larsthmn/gameshow-buzzer/src/credentials.h

//
// Created by Lars on 10.05.2024.
//

#ifndef ESP32_BUZZER_CREDENTIALS_H
#define ESP32_BUZZER_CREDENTIALS_H

#define WIFI_SSID "ssid"
#define WIFI_PASSWORD "password"
#define FTP_USER     "ftp"
#define FTP_PASSWORD "ftp"

#endif //ESP32_BUZZER_CREDENTIALS_H
