larsthmn/gameshow-buzzer/samples/audioplayback.cpp

//
// Created by Lars on 04.05.2024.
//

#if 0
#include "audioplayback.h"

#include "Arduino.h"
#include "WiFi.h"
#include "Audio.h"
#include "pins.h"

static Audio audio;

//****************************************************************************************
//                                   A U D I O _ T A S K                                 *
//****************************************************************************************

struct audioMessage{
   uint8_t     cmd;
   const char* txt;
   uint32_t    value;
   uint32_t    ret;
} audioTxMessage, audioRxMessage;

enum : uint8_t { SET_VOLUME, GET_VOLUME, CONNECTTOHOST, CONNECTTOSD };

QueueHandle_t audioSetQueue = NULL;
QueueHandle_t audioGetQueue = NULL;

static void CreateQueues(){
   audioSetQueue = xQueueCreate(10, sizeof(struct audioMessage));
   audioGetQueue = xQueueCreate(10, sizeof(struct audioMessage));
}

static void audioTask(void *parameter) {
   CreateQueues();
   if(!audioSetQueue || !audioGetQueue){
      log_e("queues are not initialized");
      while(true){;}  // endless loop
   }

   struct audioMessage audioRxTaskMessage;
   struct audioMessage audioTxTaskMessage;

   audio.setPinout(I2S_BCLK, I2S_LRC, I2S_DOUT);
   audio.setVolume(15); // 0...21

   while(true){
      if(xQueueReceive(audioSetQueue, &audioRxTaskMessage, 1) == pdPASS) {
         if(audioRxTaskMessage.cmd == SET_VOLUME){
            audioTxTaskMessage.cmd = SET_VOLUME;
            audio.setVolume(audioRxTaskMessage.value);
            audioTxTaskMessage.ret = 1;
            xQueueSend(audioGetQueue, &audioTxTaskMessage, portMAX_DELAY);
         }
         else if(audioRxTaskMessage.cmd == CONNECTTOHOST){
            audioTxTaskMessage.cmd = CONNECTTOHOST;
            audioTxTaskMessage.ret = audio.connecttohost(audioRxTaskMessage.txt);
            xQueueSend(audioGetQueue, &audioTxTaskMessage, portMAX_DELAY);
         }
         else if(audioRxTaskMessage.cmd == CONNECTTOSD){
            audioTxTaskMessage.cmd = CONNECTTOSD;
            audioTxTaskMessage.ret = audio.connecttoSD(audioRxTaskMessage.txt);
            xQueueSend(audioGetQueue, &audioTxTaskMessage, portMAX_DELAY);
         }
         else if(audioRxTaskMessage.cmd == GET_VOLUME){
            audioTxTaskMessage.cmd = GET_VOLUME;
            audioTxTaskMessage.ret = audio.getVolume();
            xQueueSend(audioGetQueue, &audioTxTaskMessage, portMAX_DELAY);
         }
         else{
            log_i("error");
         }
      }
      audio.loop();
      if (!audio.isRunning()) {
         sleep(1);
      }
   }
}

void audioInit() {
//   xTaskCreatePinnedToCore(
//      audioTask,             /* Function to implement the task */
//      "audioplay",           /* Name of the task */
//      5000,                  /* Stack size in words */
//      NULL,                  /* Task input parameter */
//      2 | portPRIVILEGE_BIT, /* Priority of the task */
//      NULL,                  /* Task handle. */
//      1                      /* Core where the task should run */
//   );
}

static audioMessage transmitReceive(audioMessage msg){
   xQueueSend(audioSetQueue, &msg, portMAX_DELAY);
   if(xQueueReceive(audioGetQueue, &audioRxMessage, portMAX_DELAY) == pdPASS){
      if(msg.cmd != audioRxMessage.cmd){
         log_e("wrong reply from message queue");
      }
   }
   return audioRxMessage;
}

void audioSetVolume(uint8_t vol){
   audioTxMessage.cmd = SET_VOLUME;
   audioTxMessage.value = vol;
   audioMessage RX = transmitReceive(audioTxMessage);
}

uint8_t audioGetVolume(){
   audioTxMessage.cmd = GET_VOLUME;
   audioMessage RX = transmitReceive(audioTxMessage);
   return RX.ret;
}

bool audioConnecttohost(const char* host){
   audioTxMessage.cmd = CONNECTTOHOST;
   audioTxMessage.txt = host;
   audioMessage RX = transmitReceive(audioTxMessage);
   return RX.ret;
}

bool audioConnecttoSD(const char* filename){
   audioTxMessage.cmd = CONNECTTOSD;
   audioTxMessage.txt = filename;
   audioMessage RX = transmitReceive(audioTxMessage);
   return RX.ret;
}

//void audio_info(const char *info){
//   Serial.print("info        "); Serial.println(info);
//}
#endif
